azonenberg/triggercrossbar/firmware/front/main/Display.cpp

/***********************************************************************************************************************
*                                                                                                                      *
* trigger-crossbar                                                                                                     *
*                                                                                                                      *
* Copyright (c) 2023-2024 Andrew D. Zonenberg and contributors                                                         *
* All rights reserved.                                                                                                 *
*                                                                                                                      *
* Redistribution and use in source and binary forms, with or without modification, are permitted provided that the     *
* following conditions are met:                                                                                        *
*                                                                                                                      *
*    * Redistributions of source code must retain the above copyright notice, this list of conditions, and the         *
*      following disclaimer.                                                                                           *
*                                                                                                                      *
*    * Redistributions in binary form must reproduce the above copyright notice, this list of conditions and the       *
*      following disclaimer in the documentation and/or other materials provided with the distribution.                *
*                                                                                                                      *
*    * Neither the name of the author nor the names of any contributors may be used to endorse or promote products     *
*      derived from this software without specific prior written permission.                                           *
*                                                                                                                      *
* THIS SOFTWARE IS PROVIDED BY THE AUTHORS "AS IS" AND ANY EXPRESS OR IMPLIED WARRANTIES, INCLUDING, BUT NOT LIMITED   *
* TO, THE IMPLIED WARRANTIES OF MERCHANTABILITY AND FITNESS FOR A PARTICULAR PURPOSE ARE DISCLAIMED. IN NO EVENT SHALL *
* THE AUTHORS BE HELD LIABLE FOR ANY DIRECT, INDIRECT, INCIDENTAL, SPECIAL, EXEMPLARY, OR CONSEQUENTIAL DAMAGES        *
* (INCLUDING, BUT NOT LIMITED TO, PROCUREMENT OF SUBSTITUTE GOODS OR SERVICES; LOSS OF USE, DATA, OR PROFITS; OR       *
* BUSINESS INTERRUPTION) HOWEVER CAUSED AND ON ANY THEORY OF LIABILITY, WHETHER IN CONTRACT, STRICT LIABILITY, OR TORT *
* (INCLUDING NEGLIGENCE OR OTHERWISE) ARISING IN ANY WAY OUT OF THE USE OF THIS SOFTWARE, EVEN IF ADVISED OF THE       *
* POSSIBILITY OF SUCH DAMAGE.                                                                                          *
*                                                                                                                      *
***********************************************************************************************************************/

#include "frontpanel.h"
#include "Display.h"
#include <math.h>

//based on https://www.eevblog.com/forum/projects/5x7-or-7x9-dot-matrix-font-files-in-cc/msg3946252/#msg3946252
static const uint8_t g_bitmapFont5x8[] =
{
	0x00, 0x00, 0x00, 0x00, 0x00,
	0x3E, 0x5B, 0x4F, 0x5B, 0x3E,
	0x3E, 0x6B, 0x4F, 0x6B, 0x3E,
	0x1C, 0x3E, 0x7C, 0x3E, 0x1C,
	0x18, 0x3C, 0x7E, 0x3C, 0x18,
	0x1C, 0x57, 0x7D, 0x57, 0x1C,
	0x1C, 0x5E, 0x7F, 0x5E, 0x1C,
	0x00, 0x18, 0x3C, 0x18, 0x00,
	0xFF, 0xE7, 0xC3, 0xE7, 0xFF,
	0x00, 0x18, 0x24, 0x18, 0x00,
	0xFF, 0xE7, 0xDB, 0xE7, 0xFF,
	0x30, 0x48, 0x3A, 0x06, 0x0E,
	0x26, 0x29, 0x79, 0x29, 0x26,
	0x40, 0x7F, 0x05, 0x05, 0x07,
	0x40, 0x7F, 0x05, 0x25, 0x3F,
	0x5A, 0x3C, 0xE7, 0x3C, 0x5A,
	0x7F, 0x3E, 0x1C, 0x1C, 0x08,
	0x08, 0x1C, 0x1C, 0x3E, 0x7F,
	0x14, 0x22, 0x7F, 0x22, 0x14,
	0x5F, 0x5F, 0x00, 0x5F, 0x5F,
	0x06, 0x09, 0x7F, 0x01, 0x7F,
	0x00, 0x66, 0x89, 0x95, 0x6A,
	0x60, 0x60, 0x60, 0x60, 0x60,
	0x94, 0xA2, 0xFF, 0xA2, 0x94,
	0x08, 0x04, 0x7E, 0x04, 0x08,
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
	{ 0x00, 0x00, 0x00, 0x00, 0x00, 0x3e, 0x42, 0x42, 0x42, 0x42, 0x42, 0x42, 0x00, 0x00, 0x00 },	//0x6e = 'n'
	{ 0x00, 0x00, 0x00, 0x00, 0x00, 0x3c, 0x42, 0x42, 0x42, 0x42, 0x42, 0x3c, 0x00, 0x00, 0x00 },	//0x6f = 'o'

	{ 0x00, 0x00, 0x00, 0x00, 0x00, 0x3e, 0x42, 0x42, 0x42, 0x42, 0x42, 0x3e, 0x02, 0x02, 0x02 },	//0x70 = 'p'
	{ 0x00, 0x00, 0x00, 0x00, 0x00, 0x7c, 0x42, 0x42, 0x42, 0x42, 0x42, 0x7c, 0x40, 0x40, 0x40 },	//0x71 = 'q'
	{ 0x00, 0x00, 0x00, 0x00, 0x00, 0x3a, 0x06, 0x02, 0x02, 0x02, 0x02, 0x02, 0x00, 0x00, 0x00 },	//0x72 = 'r'
	{ 0x00, 0x00, 0x00, 0x00, 0x00, 0x3c, 0x42, 0x02, 0x3c, 0x40, 0x42, 0x3c, 0x00, 0x00, 0x00 },	//0x73 = 's'
	{ 0x00, 0x00, 0x00, 0x08, 0x08, 0x3e, 0x08, 0x08, 0x08, 0x08, 0x08, 0x30, 0x00, 0x00, 0x00 },	//0x74 = 't'
	{ 0x00, 0x00, 0x00, 0x00, 0x00, 0x42, 0x42, 0x42, 0x42, 0x42, 0x42, 0x7c, 0x00, 0x00, 0x00 },	//0x75 = 'u'
	{ 0x00, 0x00, 0x00, 0x00, 0x00, 0x41, 0x41, 0x22, 0x22, 0x14, 0x14, 0x08, 0x00, 0x00, 0x00 },	//0x76 = 'v'
	{ 0x00, 0x00, 0x00, 0x00, 0x00, 0x41, 0x41, 0x49, 0x49, 0x49, 0x55, 0x22, 0x00, 0x00, 0x00 },	//0x77 = 'w'
	{ 0x00, 0x00, 0x00, 0x00, 0x00, 0x41, 0x22, 0x14, 0x08, 0x14, 0x22, 0x41, 0x00, 0x00, 0x00 },	//0x78 = 'x'
	{ 0x00, 0x00, 0x00, 0x00, 0x00, 0x42, 0x42, 0x42, 0x42, 0x42, 0x62, 0x5c, 0x40, 0x20, 0x1e },	//0x79 = 'y'
	{ 0x00, 0x00, 0x00, 0x00, 0x00, 0x7e, 0x20, 0x10, 0x08, 0x04, 0x02, 0x7e, 0x00, 0x00, 0x00 },	//0x7a = 'z'
	{ 0x00, 0x00, 0x30, 0x08, 0x08, 0x08, 0x08, 0x06, 0x08, 0x08, 0x08, 0x08, 0x30, 0x00, 0x00 },	//0x7b = '{'
	{ 0x00, 0x00, 0x08, 0x08, 0x08, 0x08, 0x00, 0x08, 0x08, 0x08, 0x08, 0x08, 0x00, 0x00, 0x00 },	//0x7c = '|'
	{ 0x00, 0x00, 0x06, 0x08, 0x08, 0x08, 0x08, 0x30, 0x08, 0x08, 0x08, 0x08, 0x06, 0x00, 0x00 },	//0x7d = '}'
	{ 0x00, 0x00, 0x4c, 0x32, 0x00, 0x00, 0x00, 0x00, 0x00, 0x00, 0x00, 0x00, 0x00, 0x00, 0x00 }	//0x7e = '~'
};

////////////////////////////////////////////////////////////////////////////////////////////////////////////////////////
// Construction / destruction

Display::Display(DisplaySPIType* spi, GPIOPin* busy_n, GPIOPin* cs_n, GPIOPin* dc, GPIOPin* rst)
	: m_spi(spi)
	, m_busy_n(busy_n)
	, m_cs_n(cs_n)
	, m_dc(dc)
	, m_rst_n(rst)
	, m_width(212)
	, m_height(104)
	, m_refreshState(STATE_IDLE)
{
	//Deassert SPI CS#
	*m_cs_n = 1;

	g_log("Resetting display\n");
	g_logTimer.Sleep(1000);

	//Reset the display, need 5ms between each cycle
	*m_rst_n = 1;
	g_logTimer.Sleep(500);
	*m_rst_n = 0;
	g_logTimer.Sleep(500);
	*m_rst_n = 1;
	g_logTimer.Sleep(500);

	//wait for busy to clear

	//Soft reset
	SendCommand(0x00);
	SendData(0x0e);
	g_logTimer.Sleep(500);

	//Clear both bitplanes to blank
	Clear();
	Clear();

	//Read the OTP data
	g_log("Reading OTP...\n");
	g_logTimer.Sleep(500);
	LogIndenter li(g_log);
	SendCommand(0xa2);
	g_logTimer.Sleep(500);
	ReadData();	//dummy cycle before valid data
	int activeBank = 0;
	for(int i=0; ; i++)
	{
		auto ret = ReadData();

		//After reading the 0th address, we know what addresses the other PSRs are at
		if(i == 0)
		{
			if(ret == 0xa5)
				activeBank = 0;
			else
				activeBank = 1;

			g_log("Active OTP bank = %d\n", activeBank);
		}

		if(i == 0xc00)
		{
			if( (activeBank == 1) && (ret != 0xa5) )
			{
				g_log("Not seeing good data on OTP bank 1 either (ret = %02x), using defaults\n", ret);
				m_psr0 = 0xcf;
				m_psr1 = 0x02;
				activeBank = 2;
				break;
			}
		}

		if(activeBank == 0)
		{
			//seems there's an off-by-one where we count bytes since the 0xa5, so a5 isn't zero?
			if(i == 0xb1c)
				m_psr0 = ret;
			if(i == 0xb1d)
			{
				m_psr1 = ret;
				break;
			}
		}

		else if(activeBank == 1)
		{
			if(i == 0x171c)
				m_psr0 = ret;
			if(i == 0x171d)
			{
				m_psr1 = ret;
				break;
			}
		}
	}

	//TODO: we sometimes read this wrong
	//m_psr0 = 0x02;
	//m_psr1 = 0xfc;
	m_psr0 = 0xcf;
	m_psr1 = 0x02;
	g_log("Done (psr0 = %02x, psr1 = %02x)\n", m_psr0, m_psr1);
}

////////////////////////////////////////////////////////////////////////////////////////////////////////////////////////
// High level interface

/**
	@brief Copy the current framebuffer to the old, and reset it to blank
 */
void Display::Clear()
{
	memset(m_framebuffer, 0, sizeof(m_framebuffer));
}

/**
	@brief Draw an ASCII string

	With a 6x8 pixel font, we get 13 lines x 35.5 chars wide.
 */
void Display::Text6x8(int16_t x, int16_t y, const char* str, bool black)
{
	const int fontwidth = 5;
	const int fontheight = 8;
	const int lineheight = 8;

	int16_t xstart = x;

	while(*str != '\0')
	{
		char c = *str;

		//Handle newlines
		if(c == '\n')
		{
			x = xstart;
			y -= lineheight;
			if(y < 0)
				break;
			str ++;
			continue;
		}

		//Draw the actual character
		for(int16_t dx=0; dx<fontwidth; dx++)
		{
			uint8_t col = g_bitmapFont5x8[5*c + dx];

			for(int16_t dy=0; dy<fontheight; dy++)
			{
				if(col & (1 << dy) )
					SetPixel(x + dx, y + fontheight - dy, black);
			}
		}

		//Move to next character cell (no blank space included in this font)
		x += fontwidth + 1;

		//Line wrap to avoid going off edge of image
		if( (x + fontwidth) >= m_width)
		{
			x = xstart;
			y -= lineheight;
			if(y < 0)
				break;
		}

		//Next byte
		str ++;
	}
}

/**
	@brief Draw an ASCII string

	With an 8x16 pixel font, we get 6.5 lines x 26.5 chars wide.
 */
void Display::Text8x16(int16_t x, int16_t y, const char* str, bool black)
{
	const int fontwidth = 8;
	const int fontheight = 15;
	const int lineheight = 16;

	int16_t xstart = x;

	while(*str != '\0')
	{
		char c = *str;

		//Handle newlines
		if(c == '\n')
		{
			x = xstart;
			y -= lineheight;
			if(y < 0)
				break;
			str ++;
			continue;
		}

		//Draw the actual character
		auto& glyph = g_bitmapFont8x16[(int)c];
		for(int16_t dy=0; dy<fontheight; dy++)
		{
			uint8_t row = glyph.pixels[dy];
			for(int16_t dx=0; dx<fontwidth; dx++)
			{
				if(row & (1 << dx) )
					SetPixel(x + dx, y + fontheight - dy, black);
			}
		}

		//Move to next character cell
		x += fontwidth;

		//Line wrap to avoid going off edge of image
		if( (x + fontwidth) >= m_width)
		{
			x = xstart;
			y -= lineheight;
			if(y < 0)
				break;
		}

		//Next byte
		str ++;
	}
}

/**
	@brief Bresenham line drawing (based on pseudocode at https://en.wikipedia.org/wiki/Bresenham%27s_line_algorithm)
 */
void Display::Line(int16_t x0, int16_t y0, int16_t x1, int16_t y1, bool black)
{
	if(abs(y1 - y0) < abs(x1 - x0))
	{
		if(x0 > x1)
			LineLow(x1, y1, x0, y0, black);
		else
			LineLow(x0, y0, x1, y1, black);
	}
	else
	{
		if(y0 > y1)
			LineHigh(x1, y1, x0, y0, black);
		else
			LineHigh(x0, y0, x1, y1, black);
	}
}

/**
	@brief Shallow slope implementation
 */
void Display::LineLow(int16_t x0, int16_t y0, int16_t x1, int16_t y1, bool black)
{
	int16_t dx = x1 - x0;
	int16_t dy = y1 - y0;
	int16_t yi = 1;

	if(dy < 0)
	{
		yi = -1;
		dy = -dy;
	}

	int16_t d = 2*dy - dx;
	int16_t y = y0;

	for(int16_t x = x0; x<= x1; x++)
	{
		SetPixel(x, y, black);

		if(d > 0)
		{
			y += yi;
			d += 2*(dy-dx);
		}
		else
			d += 2*dy;
	}
}

/**
	@brief Steep slope implementation
 */
void Display::LineHigh(int16_t x0, int16_t y0, int16_t x1, int16_t y1, bool black)
{
	int16_t dx = x1 - x0;
	int16_t dy = y1 - y0;
	int16_t xi = 1;

	if(dx < 0)
	{
		xi = -1;
		dx = -dx;
	}

	int16_t d = 2*dx - dy;
	int16_t x = x0;

	for(int16_t y = y0; y<= y1; y++)
	{
		SetPixel(x, y, black);

		if(d > 0)
		{
			x += xi;
			d += 2*(dx-dy);
		}
		else
			d += 2*dx;
	}
}

/**
	@brief Axially aligned flood fill

	assumes x0 <= x1 and y0 <= y1 for now
 */
void Display::FilledRect(int16_t x0, int16_t y0, int16_t x1, int16_t y1, bool black)
{
	for(int16_t x=x0; x<=x1; x++)
	{
		for(int16_t y=y0; y<=y1; y++)
			SetPixel(x, y, black);
	}
}

////////////////////////////////////////////////////////////////////////////////////////////////////////////////////////
// Mid level interface

/**
	@brief Sets a single pixel in the framebuffer
 */
void Display::SetPixel(uint8_t x, uint8_t y, bool black)
{
	//Image scan order: bottom left to top left is first scanline
	//bottom right to top right is last scanline
	//Total format is 104 pixels / 13 bytes per scanline, 212 scanlines
	//MSB of a byte is the lowest pixel

	//Start of the column
	uint16_t coloff = x * (m_height/8);

	//Bit and byte positions
	uint8_t nbyte = y / 8;
	uint8_t nbit = 7 - (y % 8);
	uint8_t bitmask = (1 << nbit);

	//Do the actual write operations
	if(black)
		m_framebuffer[coloff + nbyte] |= bitmask;
	else
		m_framebuffer[coloff + nbyte] &= ~bitmask;
}

/**
	@brief Called each iteration of the main loop
 */
void Display::Iteration()
{
	if(!IsRefreshInProgress())
		return;

	//See what needs doing
	switch(m_refreshState)
	{
		////////////////////////////////////////////////////////////////////////////////////////////////////////////////
		// Fast path

		//Soft reset
		case STATE_REFRESH_FAST_INIT:
			g_log("fast refresh\n");

			SendCommand(0x00);
			SendData(0x0e);

			m_refreshState = STATE_REFRESH_FAST_INIT2;
			break;

		//Send initial commands
		case STATE_REFRESH_FAST_INIT2:
			if(*m_busy_n)
			{
				//Get temperature and clamp to valid range
				auto temp = ReadThermalSensor(g_tempI2cAddress);
				if(temp > 60)
					temp = 60;

				//Send temperature
				SendCommand(0xe5);
				SendData( (temp >> 8) + 0x40 );

				//Activate temperature
				SendCommand(0xe0);
				SendData(0x02);

				//Send panel settings
				SendCommand(0x00);
				SendData(m_psr0 | 0x10);
				SendData(m_psr1 | 0x02);

				//Vcom and data interval
				SendCommand(0x50);
				SendData(0x07);

				//Border setting
				SendCommand(0x50);
				SendData(0x27);

				m_refreshState = STATE_REFRESH_FAST_DATA0;
			}

			break;

		//Send old data
		case STATE_REFRESH_FAST_DATA0:
			SendCommand(0x10);
			for(int32_t i=0; i<2756; i++)
				SendData(m_oldFramebuffer[i]);

			m_refreshState = STATE_REFRESH_FAST_DATA1;
			break;

		//Send new data
		case STATE_REFRESH_FAST_DATA1:
			SendCommand(0x13);
			for(int32_t i=0; i<2756; i++)
				SendData(m_framebuffer[i]);

			m_refreshState = STATE_REFRESH_FINAL1;
			break;

		////////////////////////////////////////////////////////////////////////////////////////////////////////////////
		// Slow path

		//Initialization for the slow refresh path
		case STATE_REFRESH_SLOW_INIT:
			g_log("slow refresh\n");
			{
				//Get temperature and clamp to valid range
				auto temp = ReadThermalSensor(g_tempI2cAddress);
				if(temp > 60)
					temp = 60;

				//Send temperature
				SendCommand(0xe5);
				SendData(temp >> 8);

				//Activate temperature
				SendCommand(0xe0);
				SendData(0x02);

				//Send panel settings
				SendCommand(0x00);
				SendData(m_psr0);
				SendData(m_psr1);

				m_refreshState = STATE_REFRESH_SLOW_DATA0;
			}
			break;

		//Send the first block of data
		case STATE_REFRESH_SLOW_DATA0:
			SendCommand(0x10);
			for(int32_t i=0; i<2756; i++)
				SendData(m_framebuffer[i]);

			m_refreshState = STATE_REFRESH_SLOW_DATA1;
			break;

		//Send zeroes
		case STATE_REFRESH_SLOW_DATA1:
			SendCommand(0x13);
			for(int32_t i=0; i<2756; i++)
				SendData(0x00);

			m_refreshState = STATE_REFRESH_FINAL1;
			break;

		////////////////////////////////////////////////////////////////////////////////////////////////////////////////
		// Finish the refresh

		//Wait for busy state then send power-on command
		case STATE_REFRESH_FINAL1:

			if(*m_busy_n)
			{
				SendCommand(0x04);
				m_refreshState = STATE_REFRESH_FINAL2;
			}
			break;

		//Wait for busy state then send refresh command
		case STATE_REFRESH_FINAL2:
			if(*m_busy_n)
			{
				SendCommand(0x12);
				m_refreshState = STATE_REFRESH_FINAL3;
			}
			break;

		//Wait for refresh to complete then turn off DC-DC
		case STATE_REFRESH_FINAL3:
			if(*m_busy_n)
			{
				SendCommand(0x02);
				m_refreshState = STATE_REFRESH_FINAL4;
			}
			break;

		//Wait for DC-DC to turn off then save the framebuffer
		case STATE_REFRESH_FINAL4:
			if(*m_busy_n)
			{
				memcpy(m_oldFramebuffer, m_framebuffer, sizeof(m_framebuffer));

				SendCommand(0x00);
				SendData(0x0e);

				m_refreshState = STATE_IDLE;
			}
			break;

		default:
			break;
	}
}

/**
	@brief Push the framebuffer to the display
 */
void Display::StartRefresh(bool forceFullScreenUpdate)
{
	if(forceFullScreenUpdate)
		m_refreshState = STATE_REFRESH_SLOW_INIT;
	else
		m_refreshState = STATE_REFRESH_FAST_INIT;
}

////////////////////////////////////////////////////////////////////////////////////////////////////////////////////////
// Low level interface

void Display::SendCommand(uint8_t cmd)
{
	*m_dc = 0;
	*m_cs_n = 0;

	m_spi->BlockingWrite(cmd);
	m_spi->WaitForWrites();
	m_spi->DiscardRxData();

	*m_cs_n = 1;
}

void Display::SendData(uint8_t data)
{
	*m_dc = 1;
	*m_cs_n = 0;

	m_spi->BlockingWrite(data);
	m_spi->WaitForWrites();
	m_spi->DiscardRxData();

	*m_cs_n = 1;
}

uint8_t Display::ReadData()
{
	*m_dc = 1;
	*m_cs_n = 0;

	auto ret = m_spi->BlockingRead();


	*m_cs_n = 1;
	return ret;
}
